wilco2009/MercuryAce/Clone/Case/STL/Power Supply Jupiter Ace v1.png

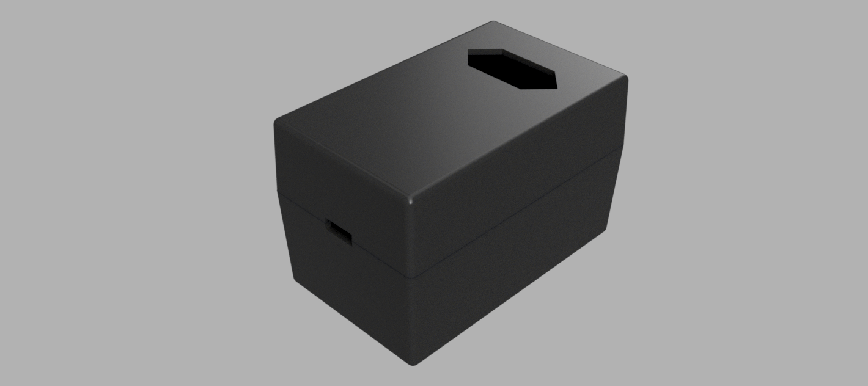
Clone/Case/STL/Power Supply Jupiter Ace v1.png
