wilco2009/MercuryAce/images/keyboard1.png

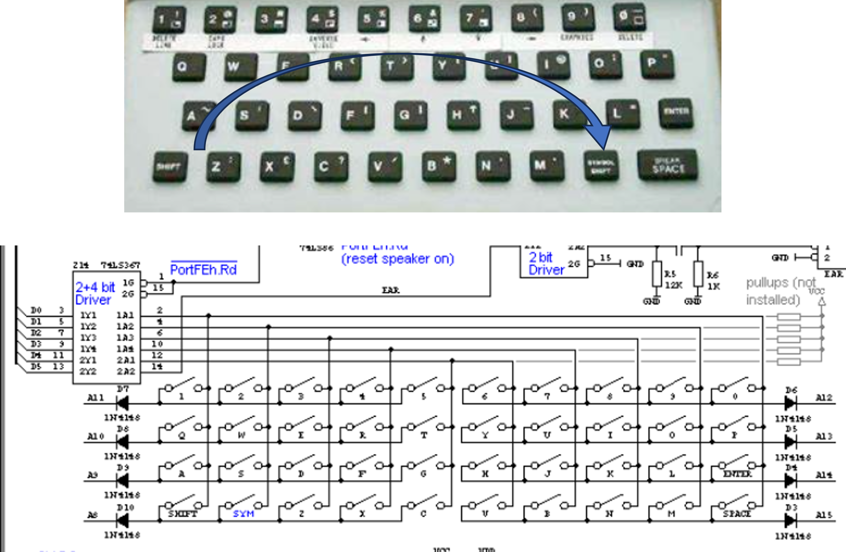
images/keyboard1.png
