wilco2009/MercuryAce/images/viden.png

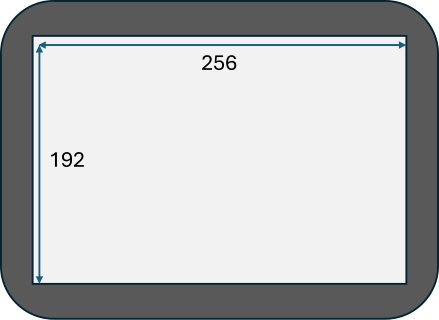
images/viden.png
